MRIgorr/Agrobot/3D models/Pictures/КорзинаСервомотор.jpg

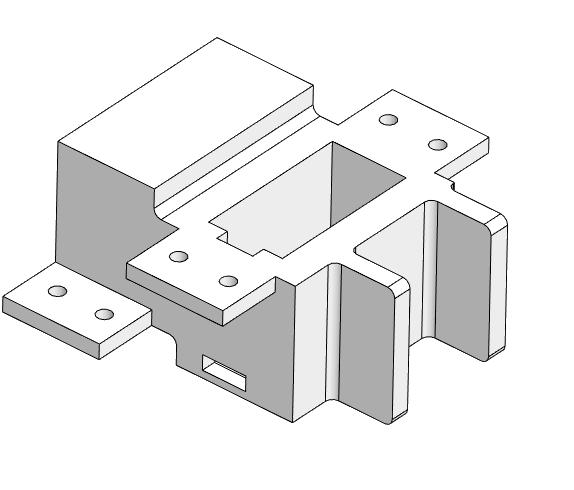
3D models/Pictures/КорзинаСервомотор.jpg
