MRIgorr/Agrobot/3D models/Pictures/КреплениеДрайвер.jpg

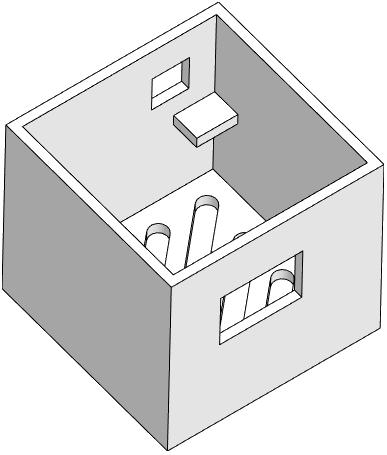
3D models/Pictures/КреплениеДрайвер.jpg
