MRIgorr/Agrobot/3D models/Pictures/КрпелениеЛезвие.jpg

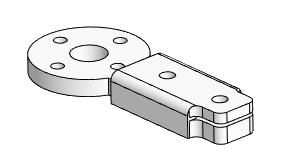
3D models/Pictures/КрпелениеЛезвие.jpg
