MRIgorr/Agrobot/3D models/Pictures/НижняяКрышкаМанипулятор.jpg

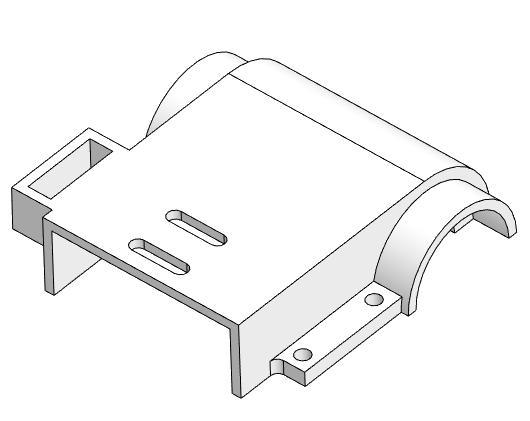
3D models/Pictures/НижняяКрышкаМанипулятор.jpg
