MRIgorr/Agrobot/3D models/Pictures/ПлатформаАрдуино.jpg

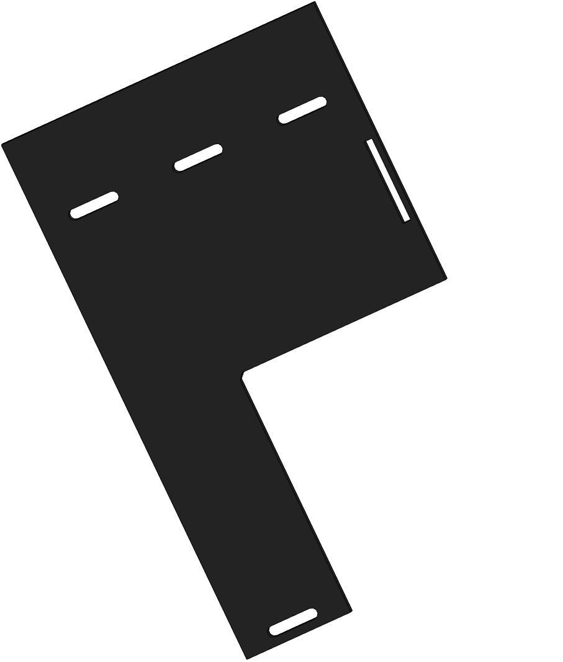
3D models/Pictures/ПлатформаАрдуино.jpg
