MRIgorr/Agrobot/3D models/Pictures/УдерживающаяКрышкаСервомотор.jpg

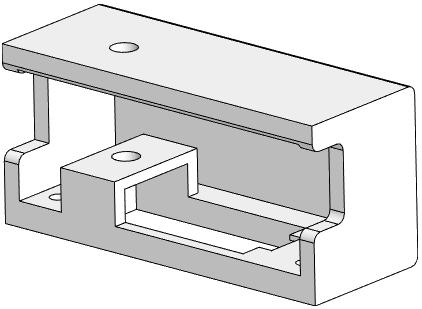
3D models/Pictures/УдерживающаяКрышкаСервомотор.jpg
