MRIgorr/Agrobot/Code Pictures/Логика управления лифтом манипулятора.jpg

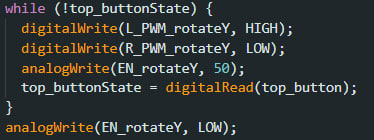
Code Pictures/Логика управления лифтом манипулятора.jpg
