MRIgorr/Agrobot/Code Pictures/Функция задачи направления и скорости моторам.jpg

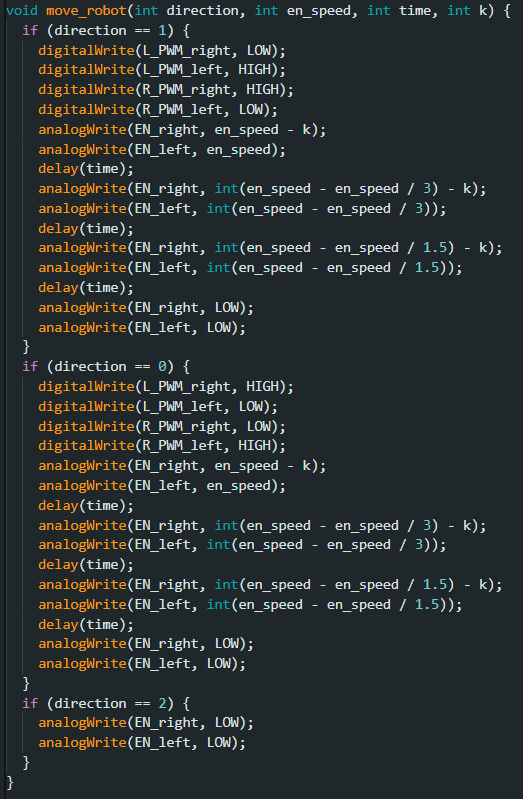
Code Pictures/Функция задачи направления и скорости моторам.jpg
