MRIgorr/Agrobot/Code Pictures/функция задачи скорости и направления. Базовый вариан.jpg

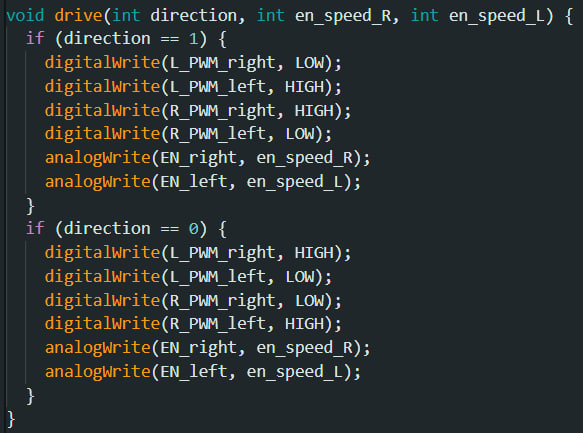
Code Pictures/функция задачи скорости и направления. Базовый вариан.jpg
