MRIgorr/Agrobot/Drawings/Корпус монтажный _ Робот - сборщик салата.jpg

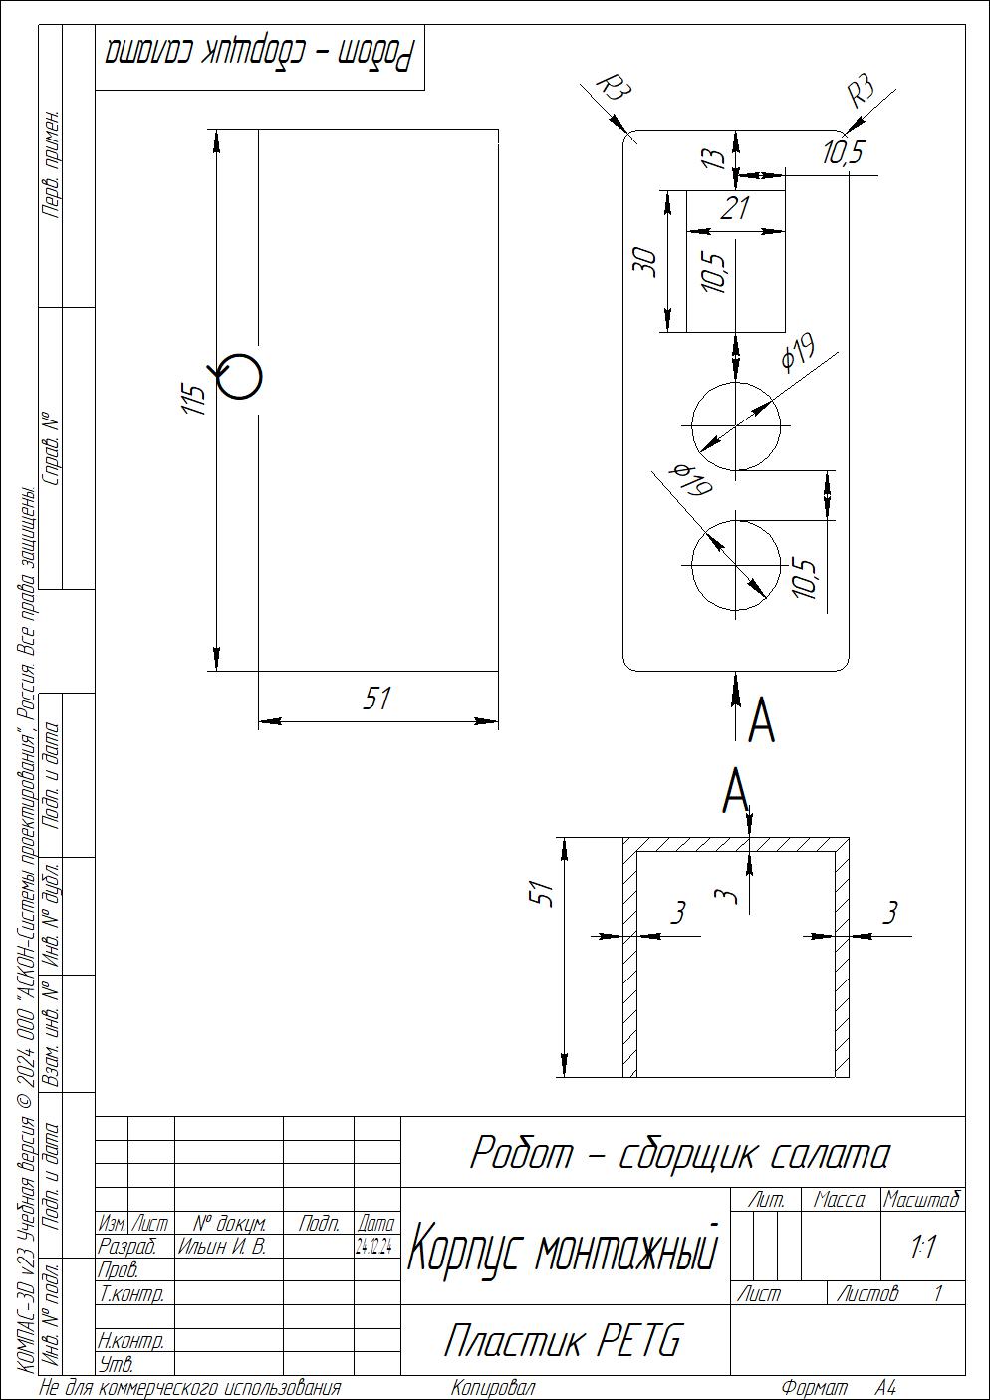
Drawings/Корпус монтажный _ Робот - сборщик салата.jpg
