MRIgorr/Agrobot/Drawings/Крепление для лезвия _ Робот - сборщик салата.jpg

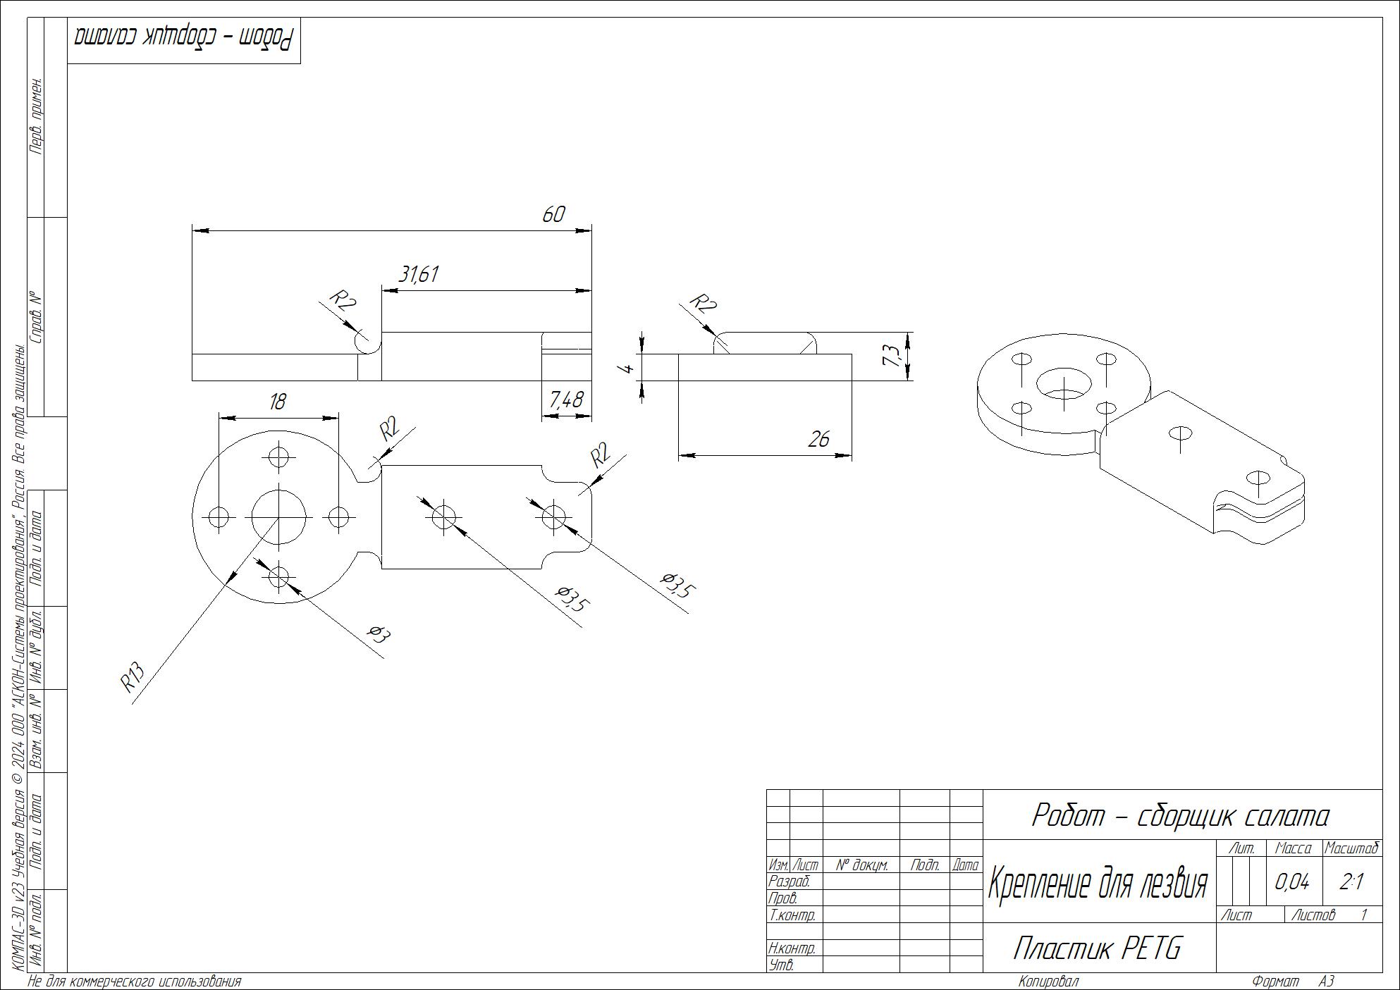
Drawings/Крепление для лезвия _ Робот - сборщик салата.jpg
