MRIgorr/Agrobot/Drawings/Крепление для сервомотора _ Робот - сборщик салата.jpg

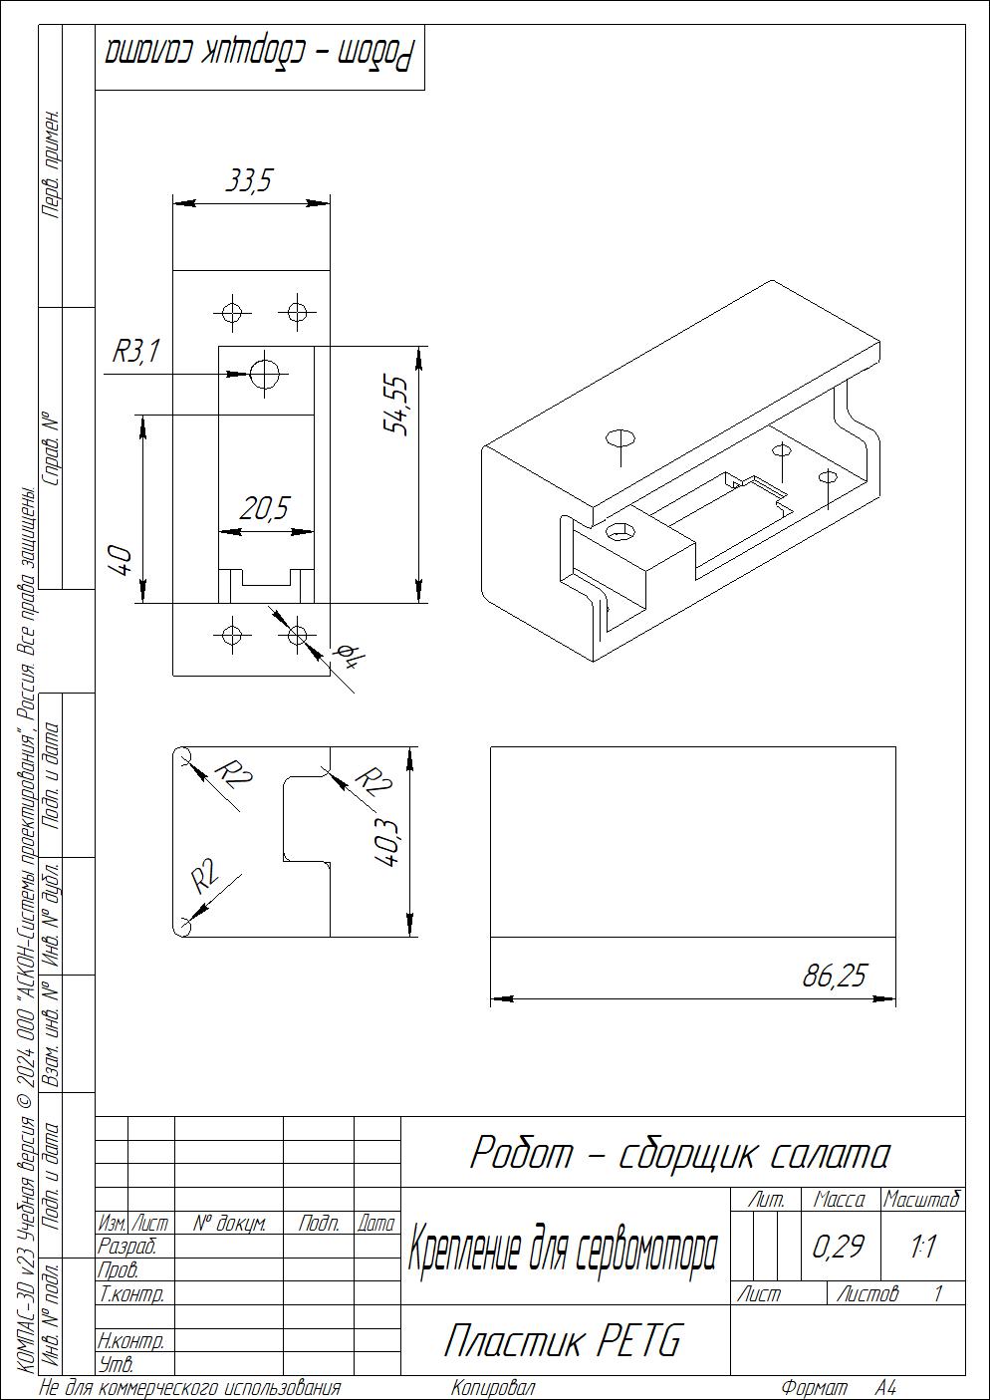
Drawings/Крепление для сервомотора _ Робот - сборщик салата.jpg
