MRIgorr/Agrobot/Drawings/Часть захвата _ Робот - сборщик салата.png

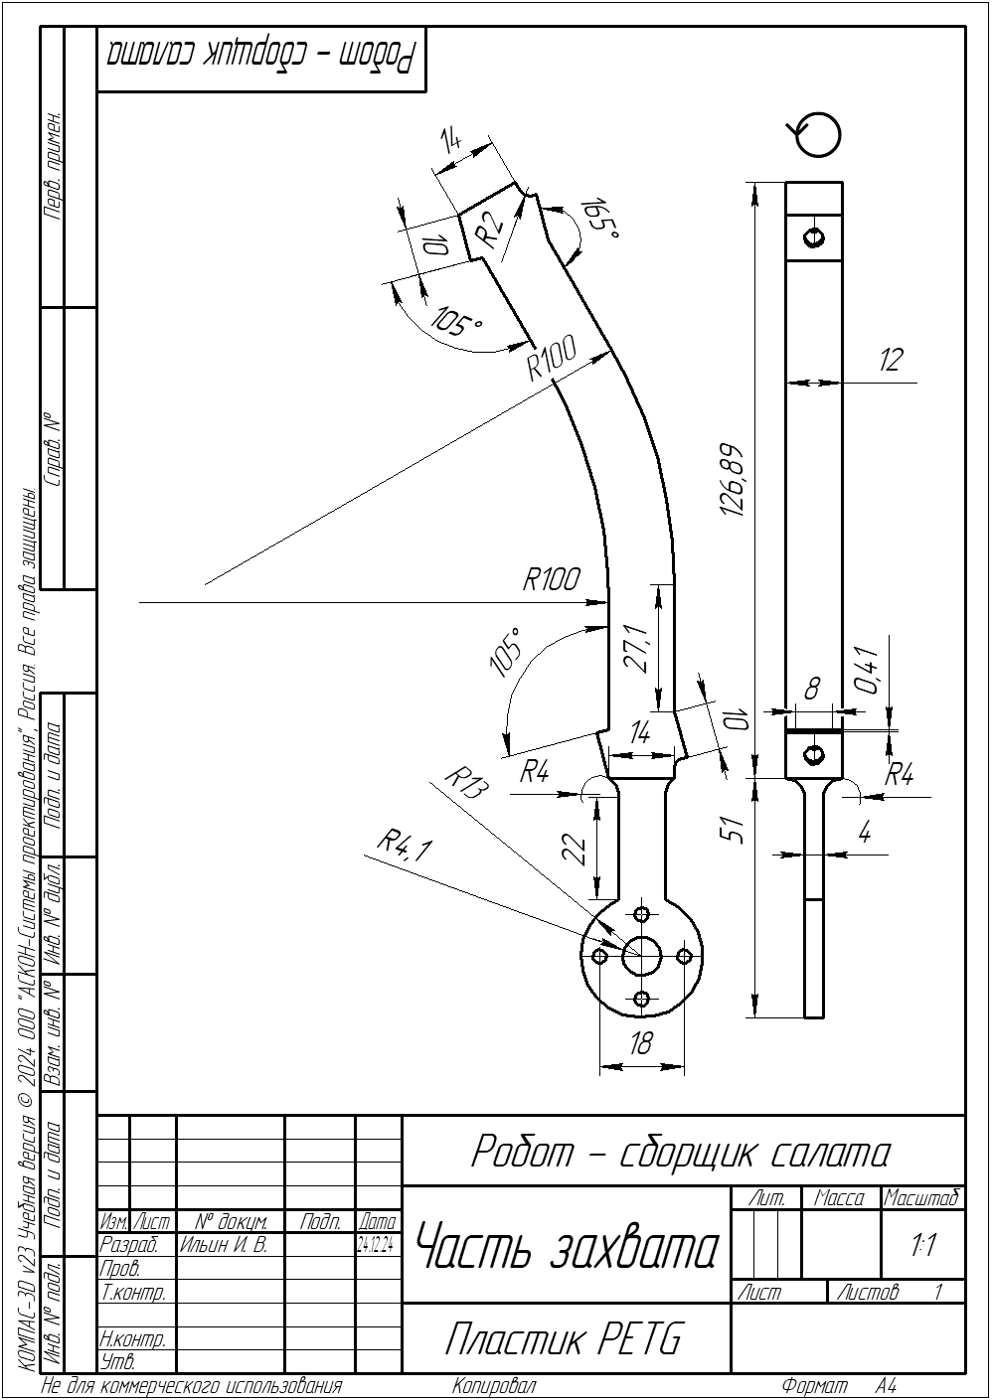
Drawings/Часть захвата _ Робот - сборщик салата.png
