MRIgorr/Agrobot/Drawings/Электрическая структурная схема.jpg

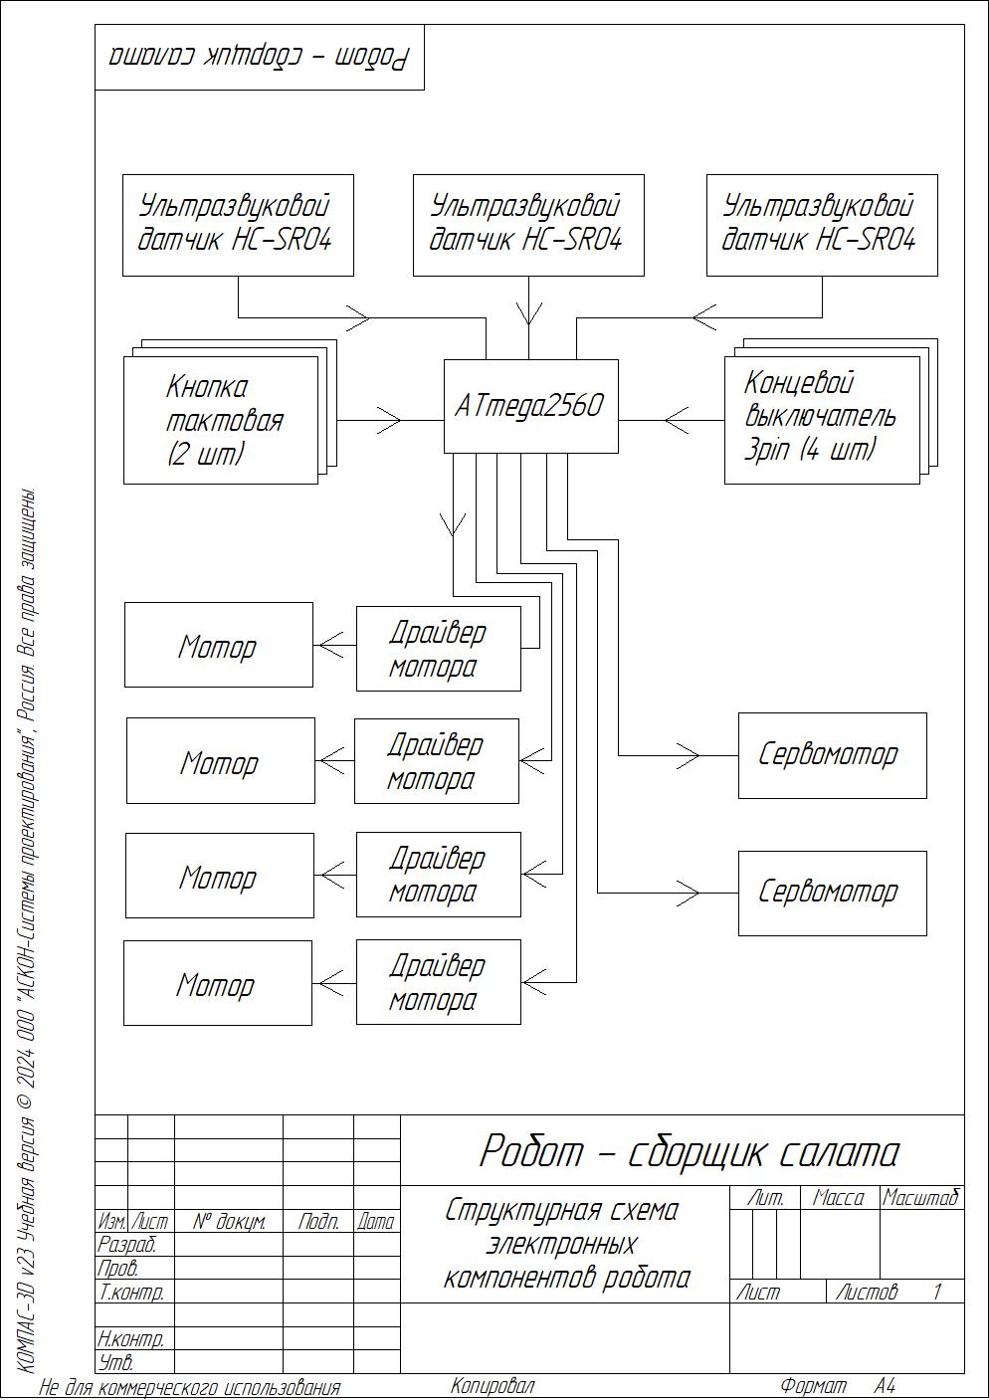
Drawings/Электрическая структурная схема.jpg
