MRIgorr/Agrobot/Pictures/Агробот для сбора салата. Расположение платы.JPG

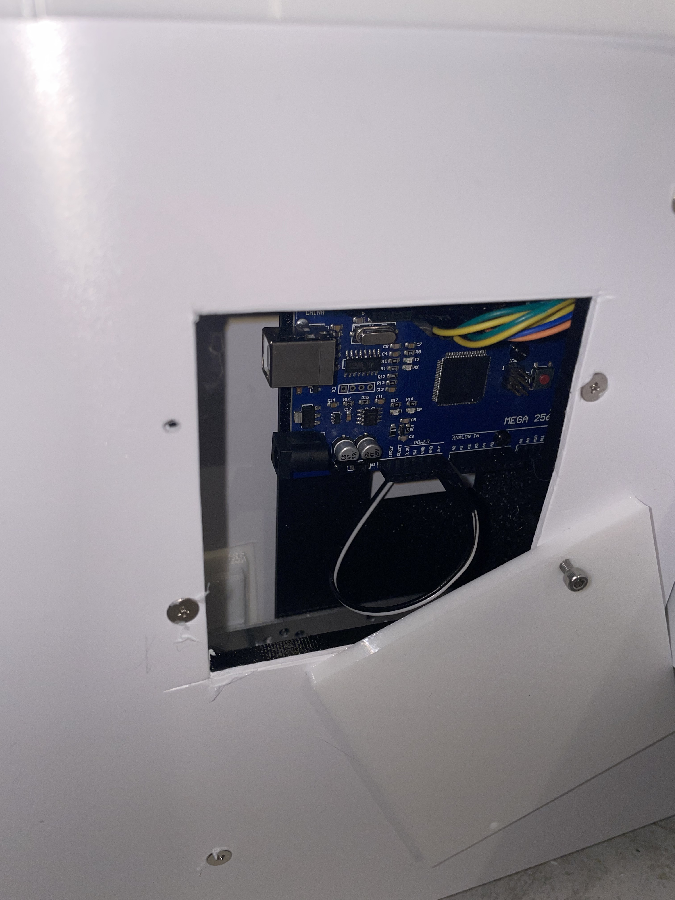
Pictures/Агробот для сбора салата. Расположение платы.JPG
