MRIgorr/Agrobot/Pictures/Первый прототип. Вид 2.JPG

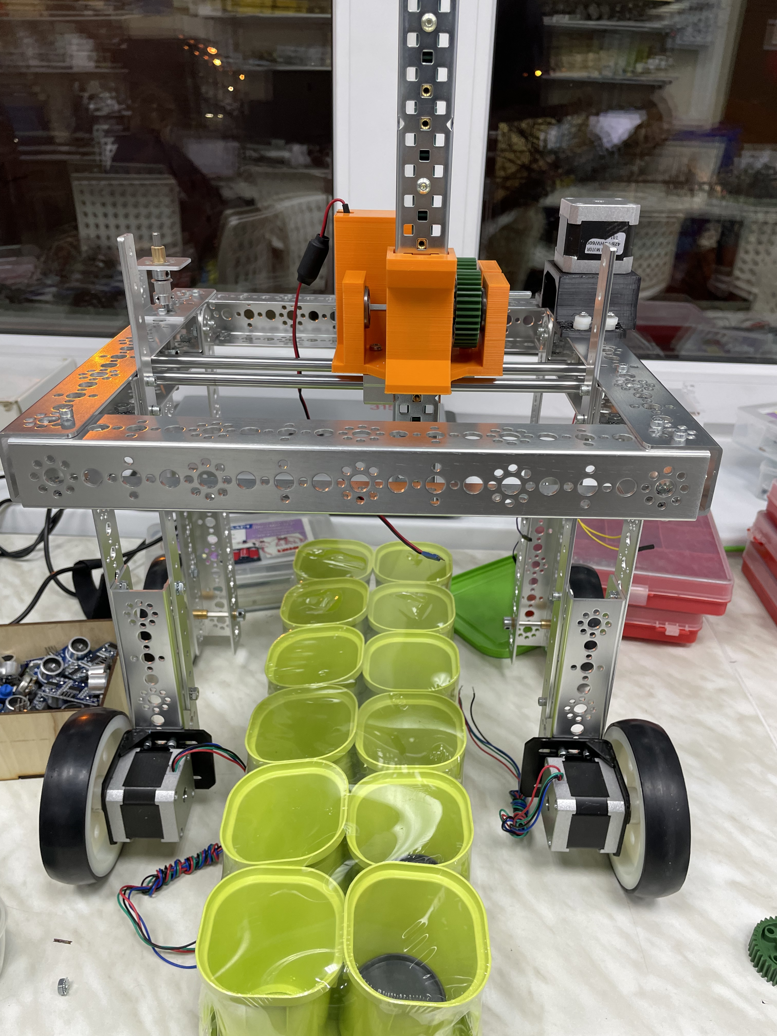
Pictures/Первый прототип. Вид 2.JPG
